uukocak/drone_trials/board_design/render_w1/iso1.png

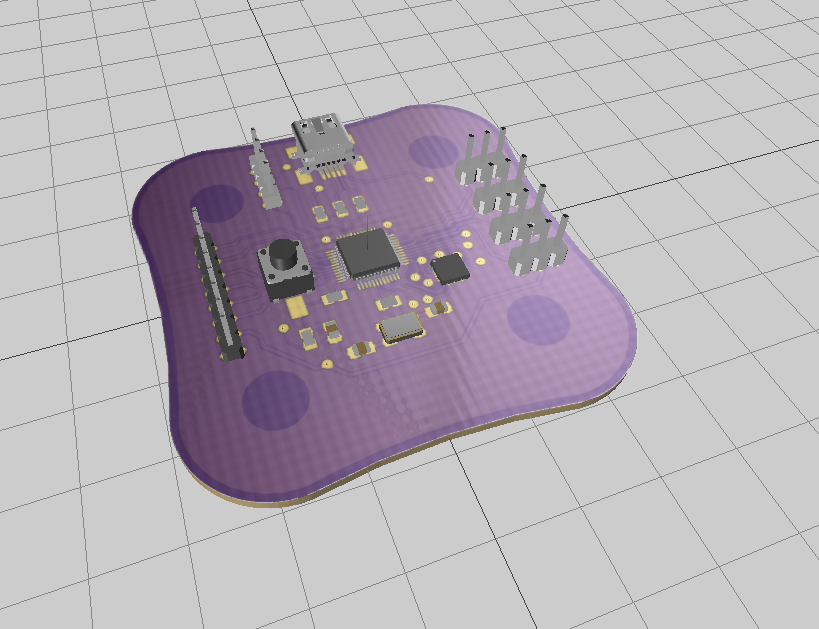
board_design/render_w1/iso1.png
