uukocak/drone_trials/board_design/render_w1s1/bot_place.png

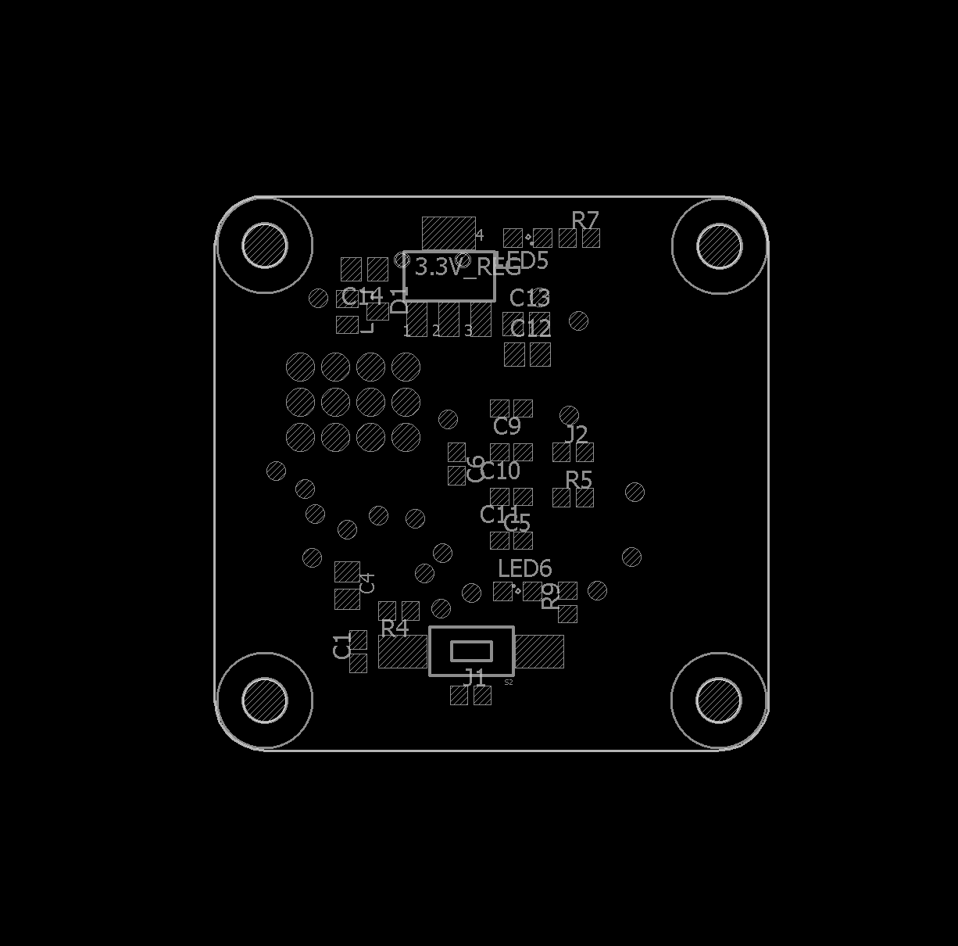
board_design/render_w1s1/bot_place.png
