uukocak/drone_trials/board_design/render_w1s1/hurf1_schematic.png

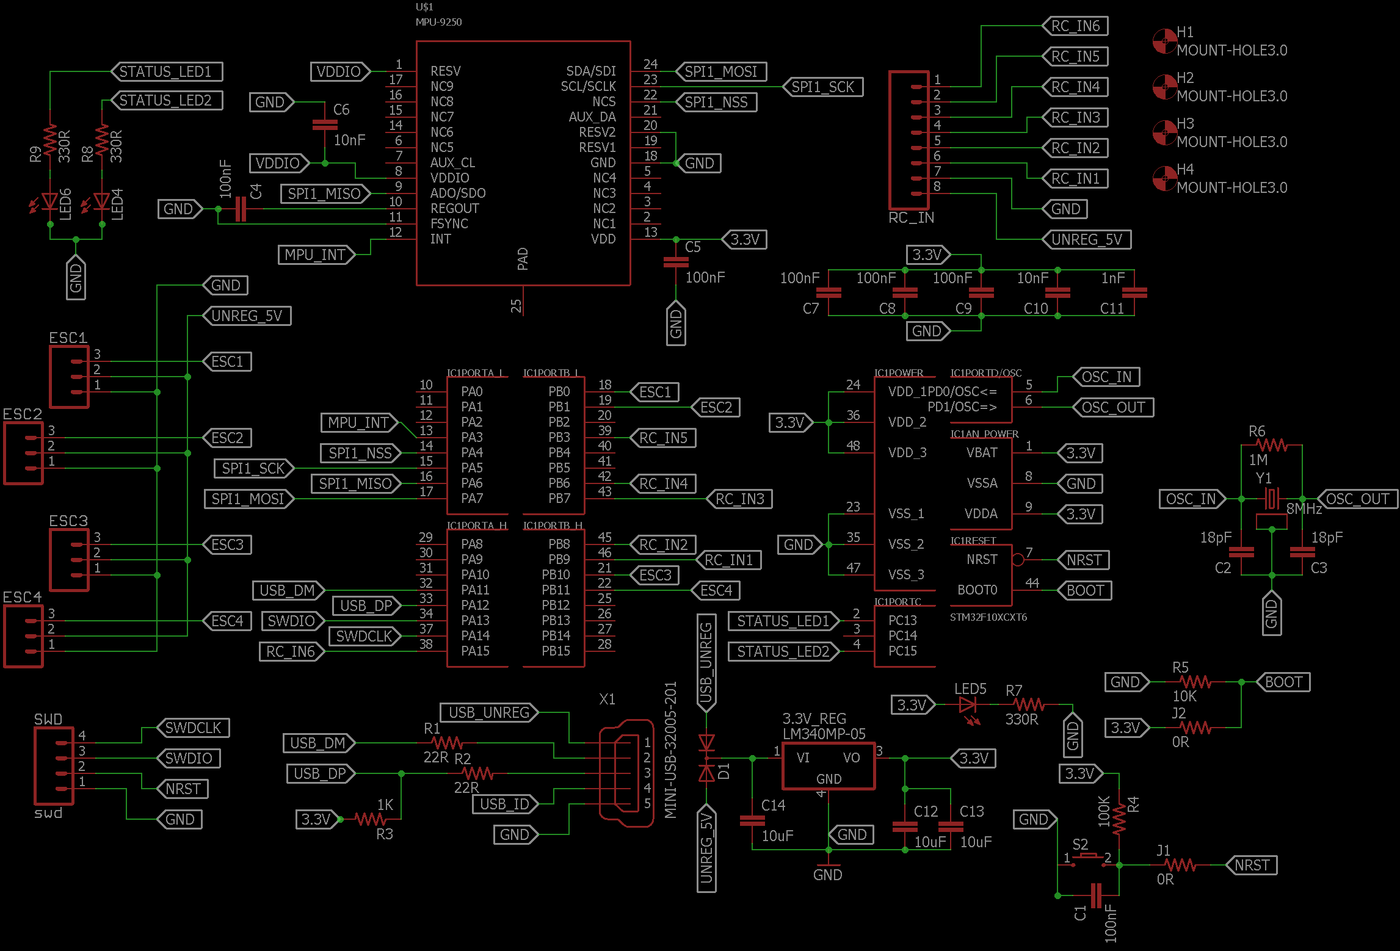
board_design/render_w1s1/hurf1_schematic.png
